Hanz-Tech/midi-adapter-hardware/photos/volca+beatstep.jpg

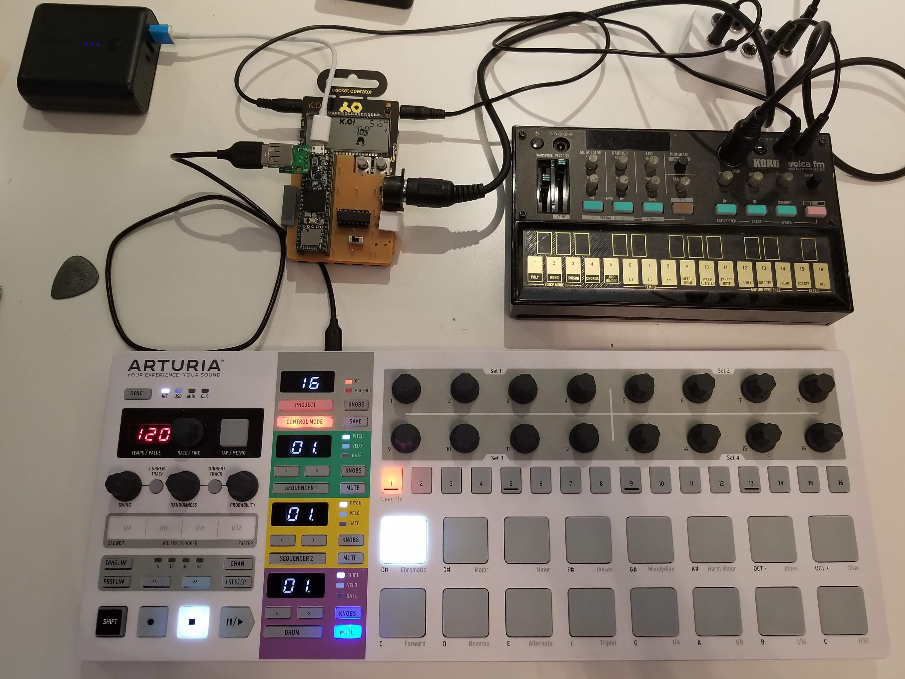
photos/volca+beatstep.jpg
