Hanz-Tech/midi-adapter-hardware/photos/assembly/3.jpg

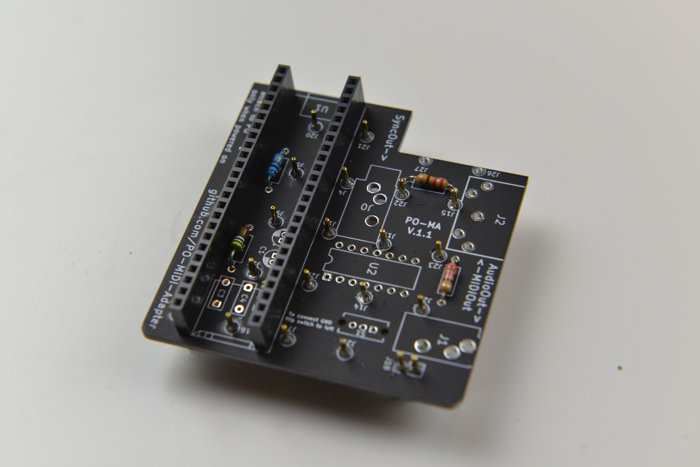
photos/assembly/3.jpg
