Hanz-Tech/midi-adapter-hardware/photos/assembly/8.JPG

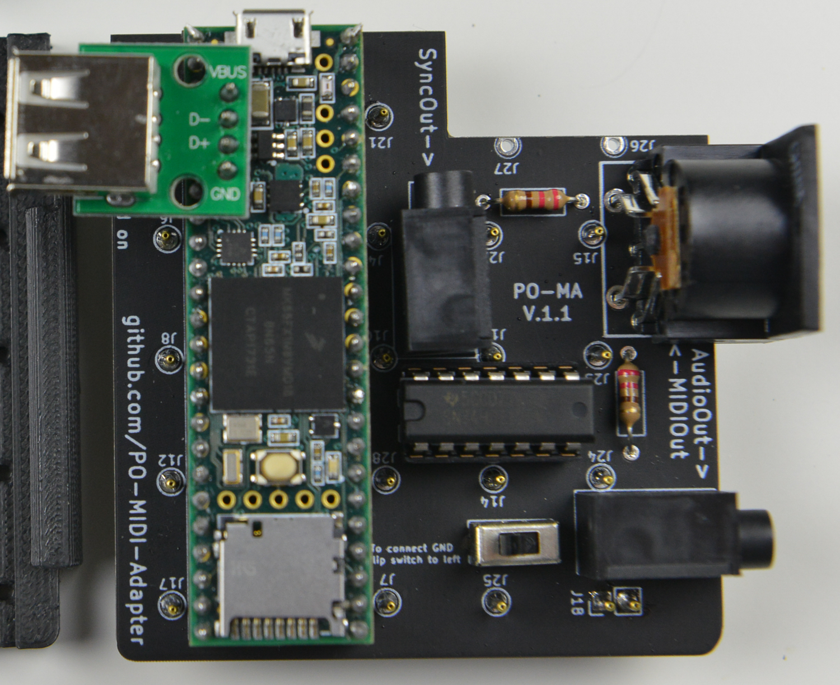
photos/assembly/8.JPG
