Hanz-Tech/midi-adapter-hardware/photos/assembly/9.JPG

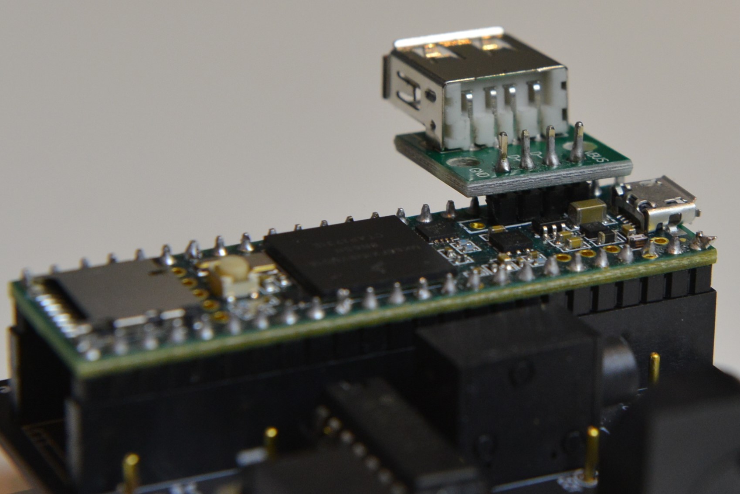
photos/assembly/9.JPG
